sabaally03/phoenix/code/forward_slave/out.ino

void OUT(void)
{
  set_bits();
  biggest();

  if (ro || ri)
  {
    while ((big_sensor_num < 8) && ( big_sensor_num >= 0))
    {

      biggest();
      set_bits();

      if (fo || fi)
      {
        if (fo) Move(9);
        else if (fi)
        {
          while (!fo)
          {

            set_bits();
            Move(9);
          }
        }
      }
      else if (bo || bi)
      {
        if (bo) Move(15);
        else if (bi)
        {
          while (!bo)
          {

            set_bits();
            Move(15);
          }
        }
      }
      else if (ro)
      {
        Move(12);
      }
      else if (ri)
      {
        while (!ro)
        {
          set_bits();
          Move(12);
        }
      }
      else
        STOP();
    }

    ////////////////////////////////////////// Khareje While /////////////////////////////////////////////////
   
    if (fo || fi)
    {
      if (fo) Move(9);
      else if (fi)
      {
        while (!fo)
        {
          set_bits();
          Move(9);
        }
      }
    }
    else if (bo || bi)
    {
      if (bo) Move(15);
      else if (bi)
      {
        while (!bo)
        {
          set_bits();
          Move(15);
        }
      }
    }
    else if (ro)
    {
      Move(12);
    }
    else if (ri)
    {
      while (!ro)
      {
        set_bits();
        Move(12);

      }
    }
    else STOP();

  }
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
    {
      if (lo) Move(1);
      else if (li)
      {
        while (!lo)
        {
          set_bits();
          Move(1);

        }
      }
    } 
    else if (bo)
    {
      Move(0);
    }
    else if (bi)
    {
      while (!bo)
      {
        set_bits();
        Move(0);

      }
    }
    else STOP();
  }

  else
  {
 follow();
  }


}
